geekmomprojects/CubeSphere/Orb4x4/Pictures/CubeBodyAndLidLabelled.JPG

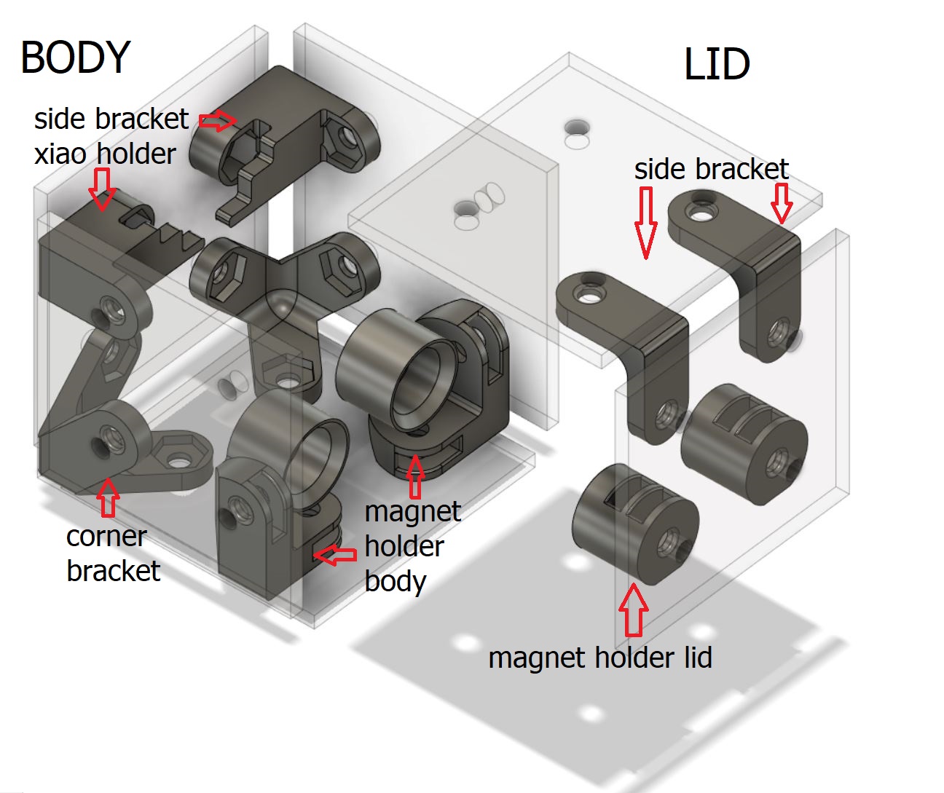
Orb4x4/Pictures/CubeBodyAndLidLabelled.JPG
