geekmomprojects/CubeSphere/Orb4x4/Pictures/CubeBodyWithoutBatteryHolder.JPG

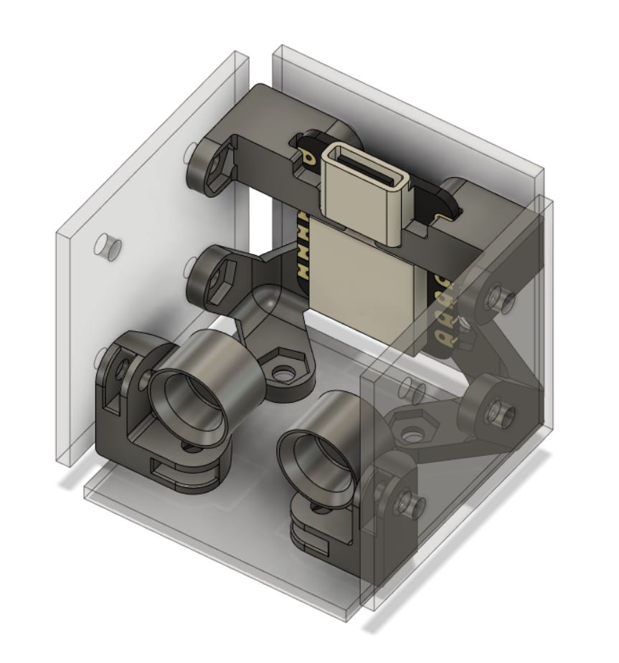
Orb4x4/Pictures/CubeBodyWithoutBatteryHolder.JPG
