geekmomprojects/CubeSphere/Orb4x4/Pictures/CubeLidWithConnectors.JPG

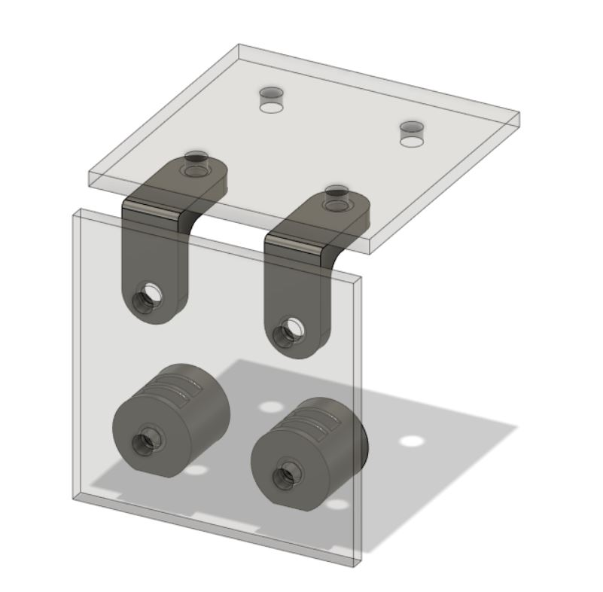
Orb4x4/Pictures/CubeLidWithConnectors.JPG
