geekmomprojects/CubeSphere/Orb5x5/Pictures/Orb5x5.JPG

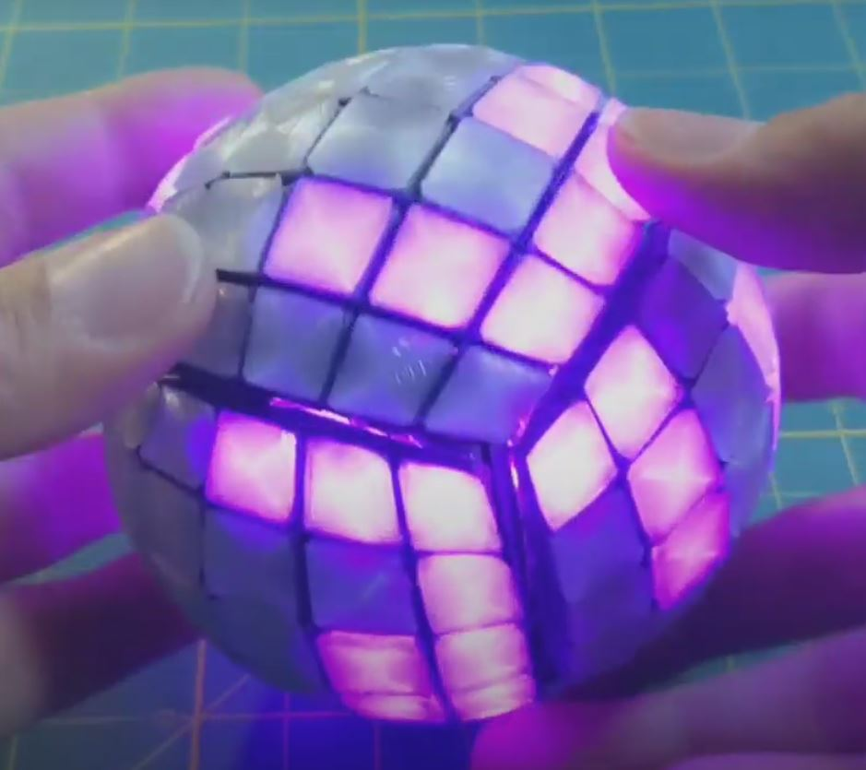
Orb5x5/Pictures/Orb5x5.JPG
