geekmomprojects/CubeSphere/Orb5x5/Pictures/OrbTiltPattern5x5.jpg

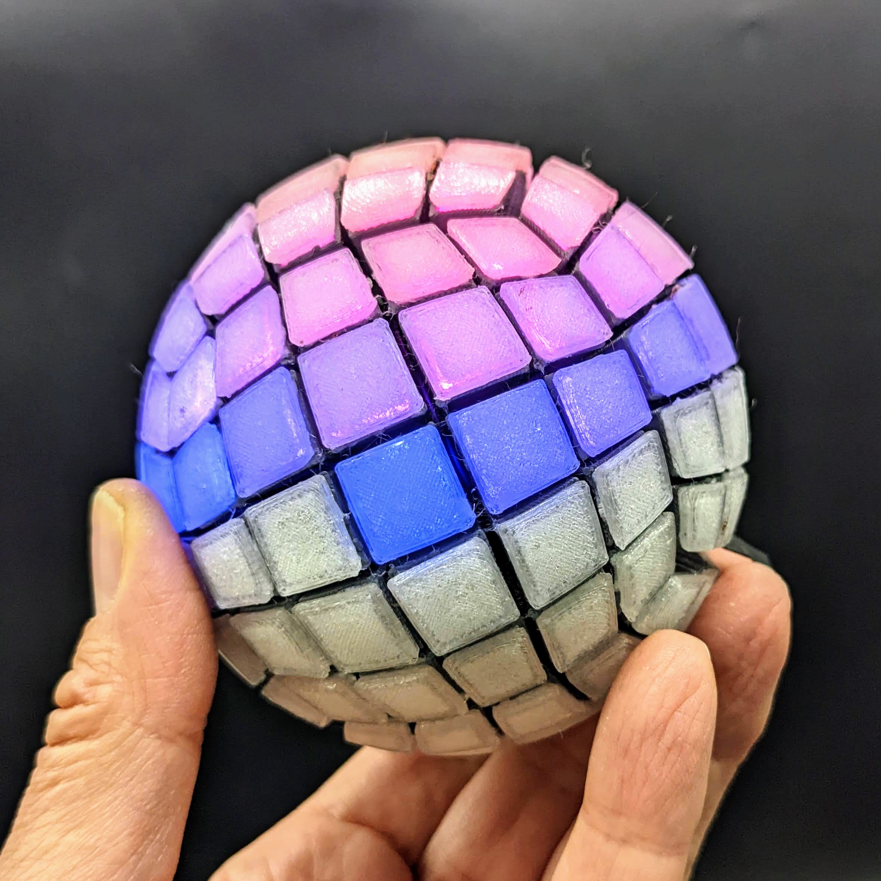
Orb5x5/Pictures/OrbTiltPattern5x5.jpg
