geekmomprojects/CubeSphere/Orb5x5/Pictures/OrbWithCube5x5.jpg

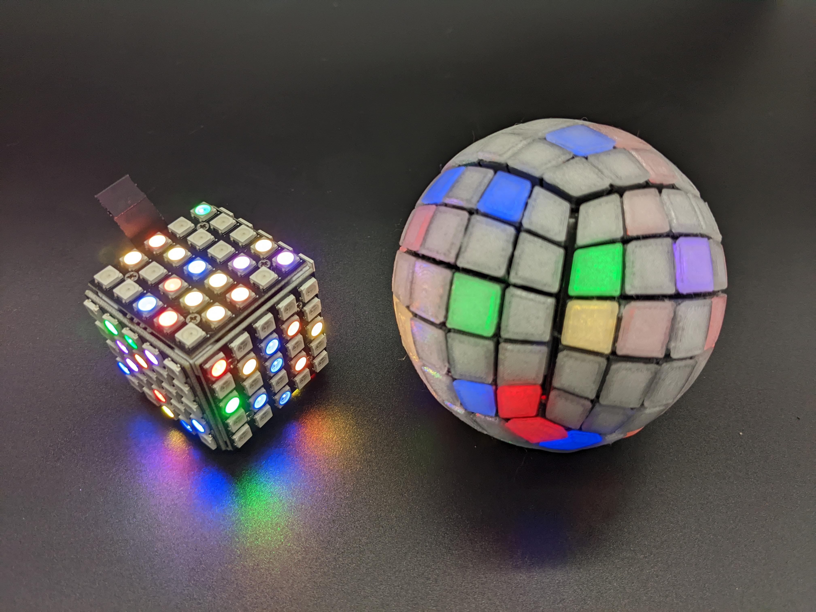
Orb5x5/Pictures/OrbWithCube5x5.jpg
