geekmomprojects/CubeSphere/Orb8x8/SK9822/Pictures/ConnectorsOnly.JPG

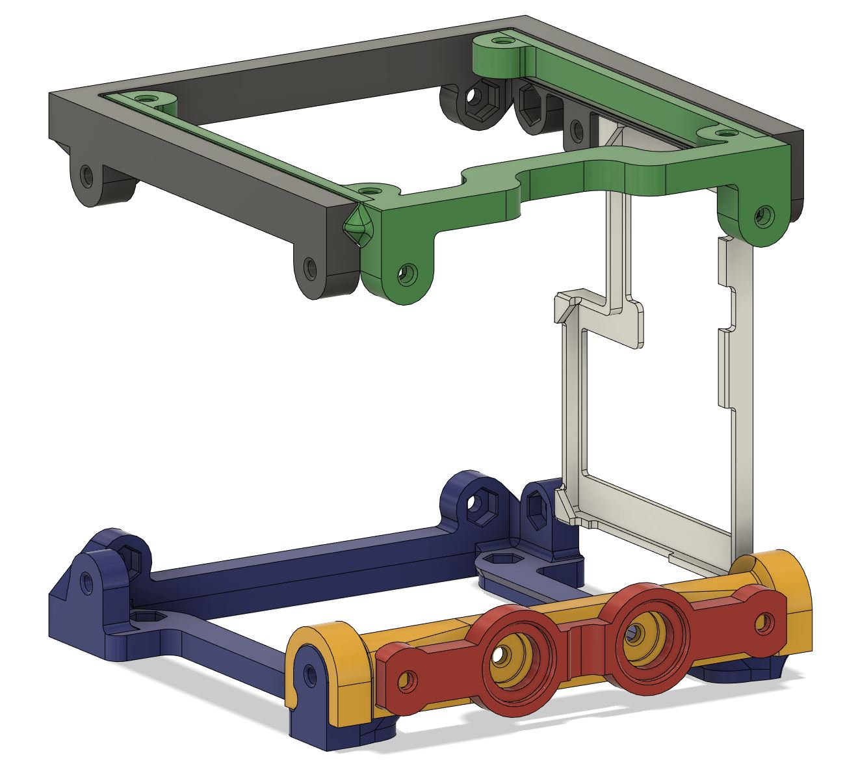
Orb8x8/SK9822/Pictures/ConnectorsOnly.JPG
