geekmomprojects/CubeSphere/Orb8x8/SK9822/Pictures/MatrixBodyWithConnectors.JPG

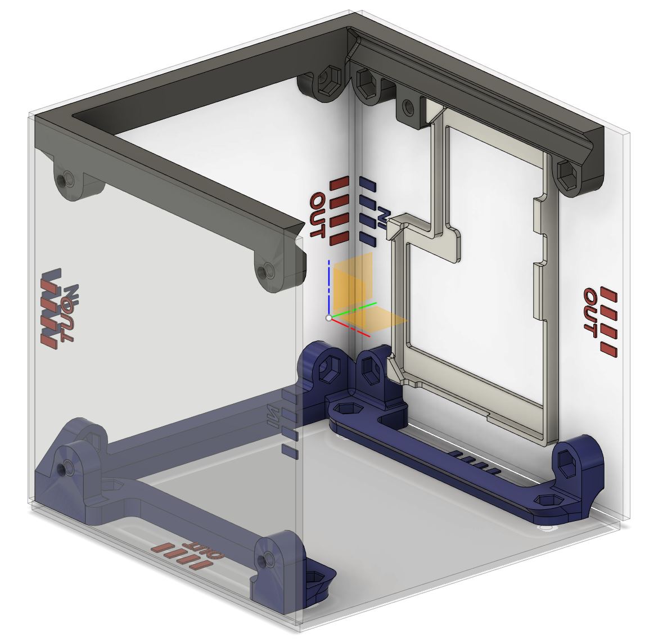
Orb8x8/SK9822/Pictures/MatrixBodyWithConnectors.JPG
