geekmomprojects/CubeSphere/Orb8x8/SK9822/Pictures/MatrixBodyWithConnectorsAndLatch.JPG

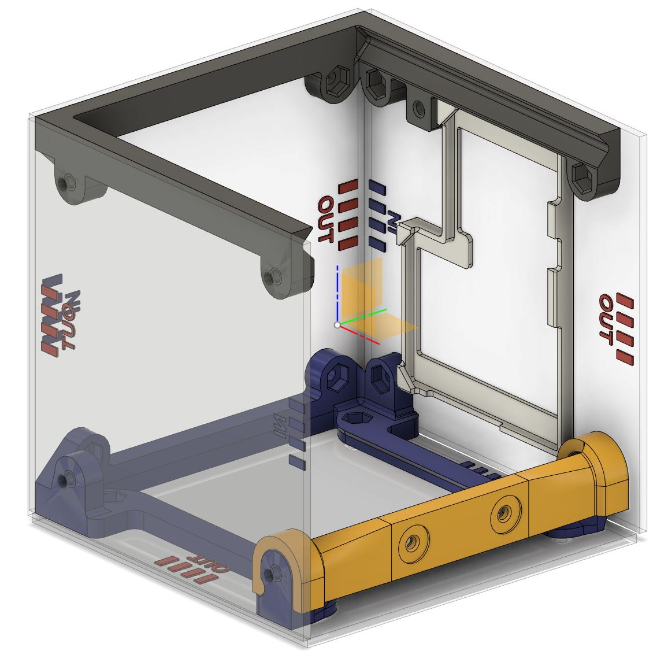
Orb8x8/SK9822/Pictures/MatrixBodyWithConnectorsAndLatch.JPG
