geekmomprojects/CubeSphere/Orb8x8/WS2812/Pictures/ConnectorsOnly.JPG

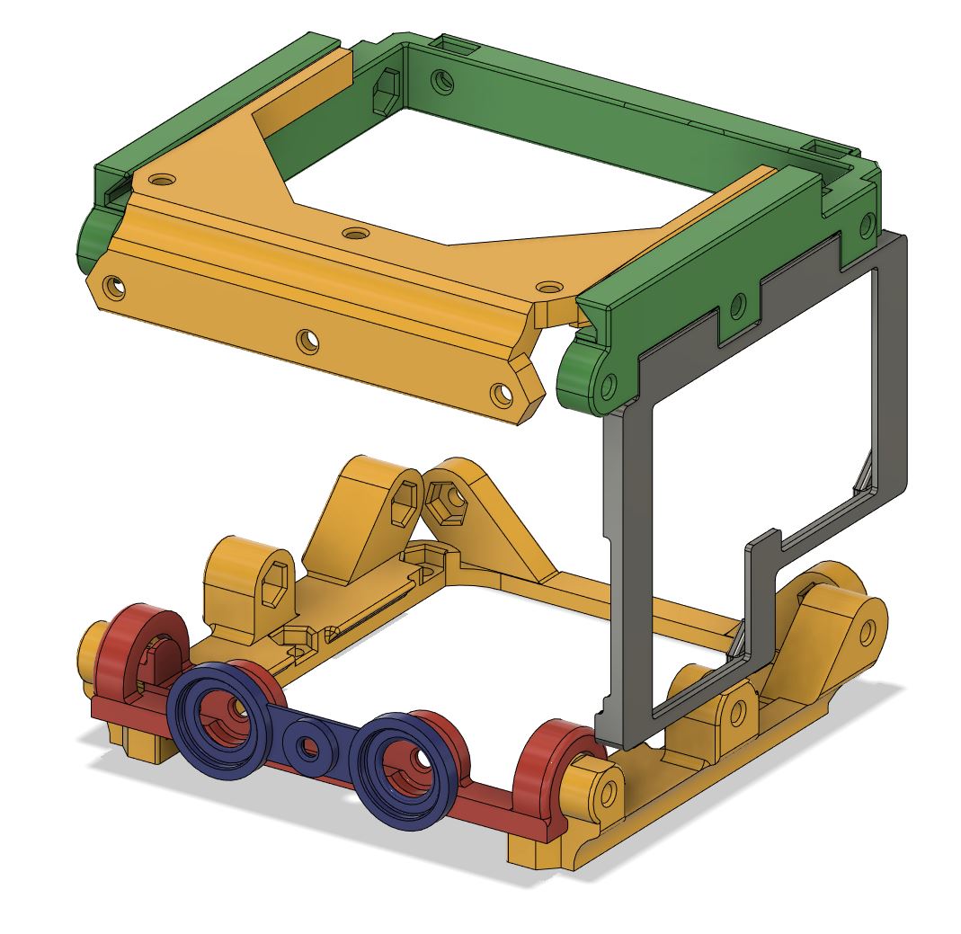
Orb8x8/WS2812/Pictures/ConnectorsOnly.JPG
