geekmomprojects/CubeSphere/Orb8x8/WS2812/Pictures/MatrixBodyLayout.JPG

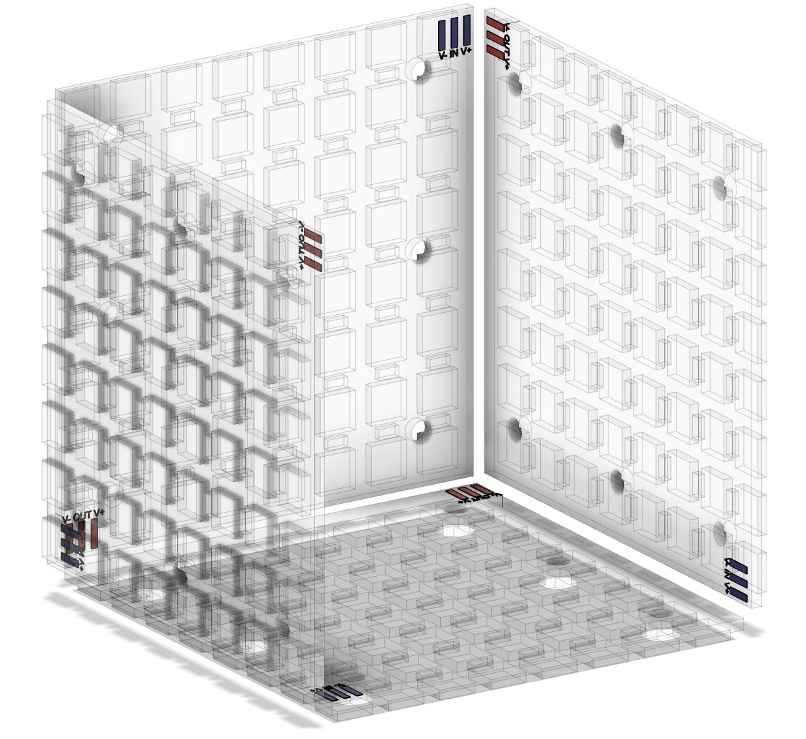
Orb8x8/WS2812/Pictures/MatrixBodyLayout.JPG
