geekmomprojects/CubeSphere/Orb8x8/WS2812/Pictures/MatrixBodyWithoutLock.JPG

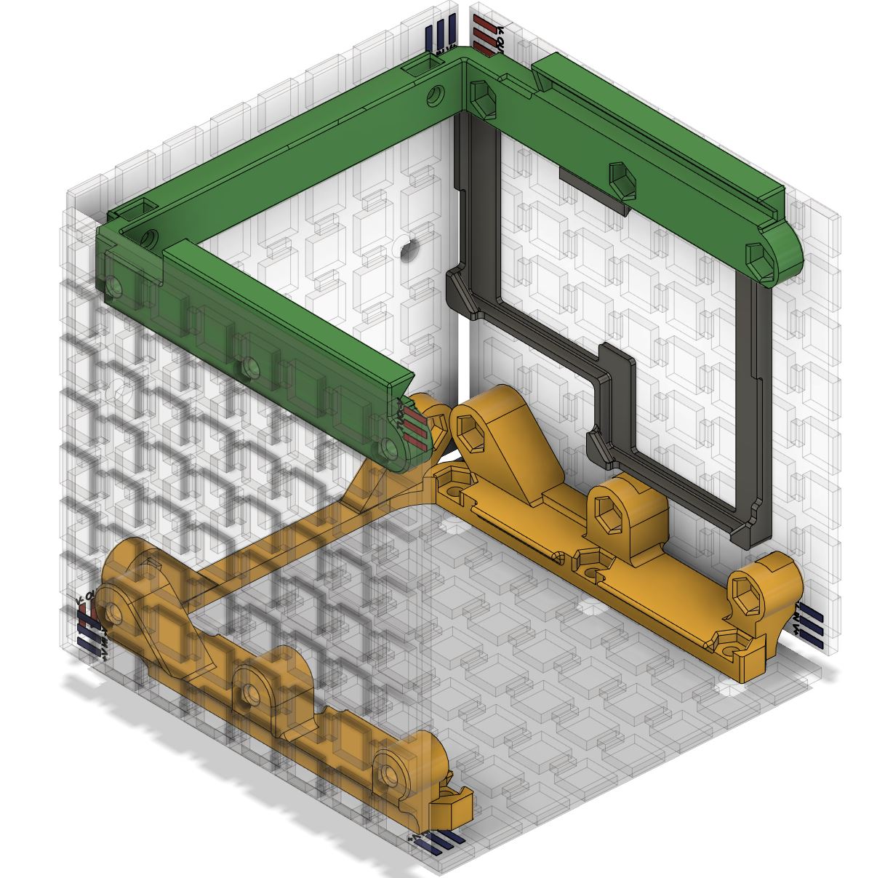
Orb8x8/WS2812/Pictures/MatrixBodyWithoutLock.JPG
