geekmomprojects/CubeSphere/Orb8x8/WS2812/Pictures/MatrixLid.JPG

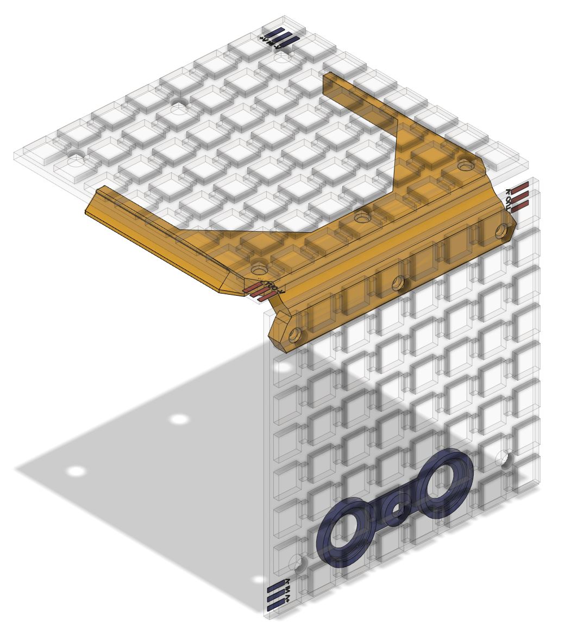
Orb8x8/WS2812/Pictures/MatrixLid.JPG
