geekmomprojects/CubeSphere/Orb8x8/WS2812/Pictures/Orb8x8.jpg

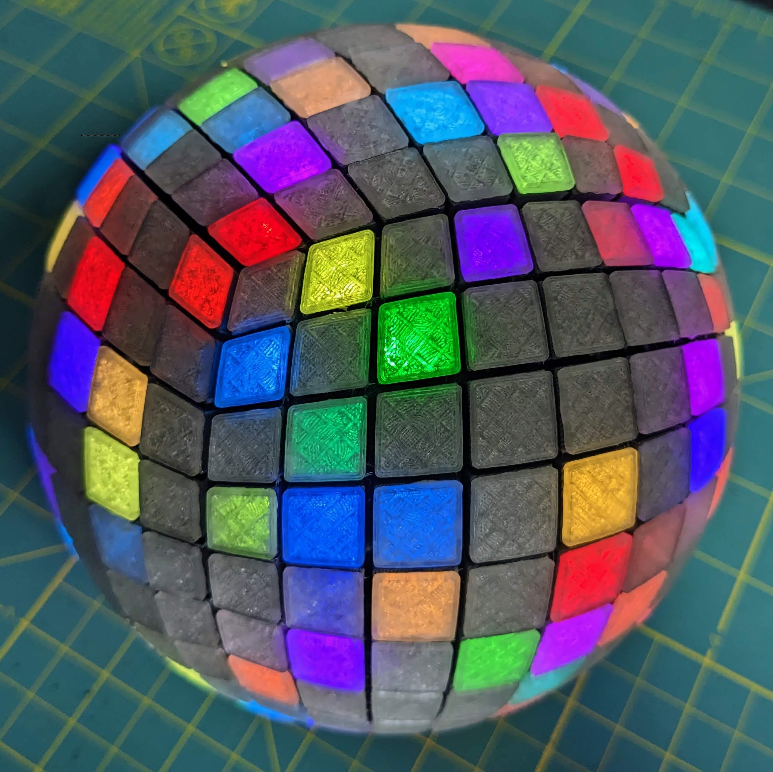
Orb8x8/WS2812/Pictures/Orb8x8.jpg
