geekmomprojects/CubeSphere/Orb5x5/Design/BatteryHolder16340.stl

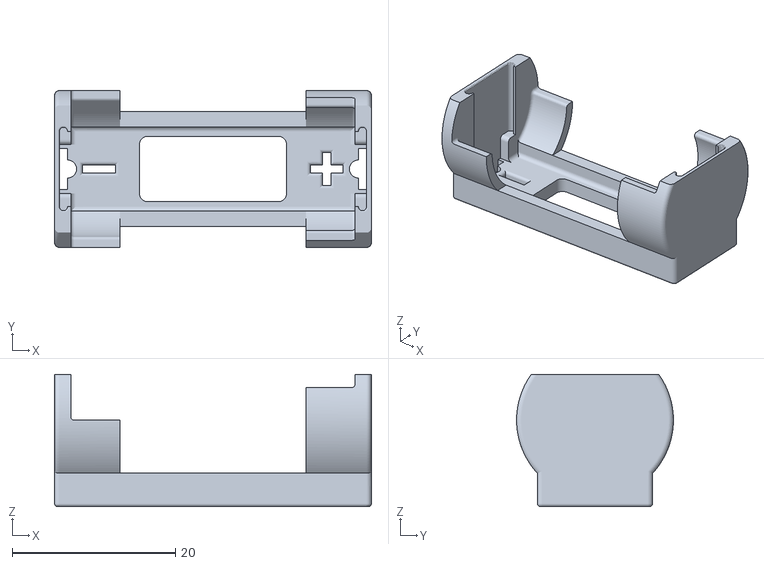
[picture p46: CAD file, 2022-10-06]
Orb5x5/Design/BatteryHolder16340.stl
38.8 x 19.2 x 16.2
