geekmomprojects/CubeSphere/Orb4x4_V2/Design/BatHolder.stl

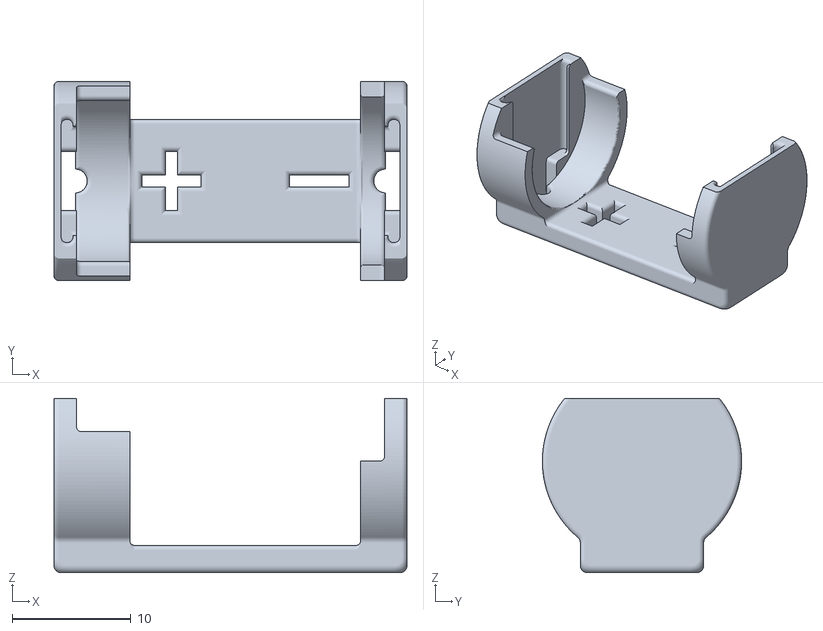
[picture p47: CAD file, 2022-10-06, an earlier design]
Orb4x4_V2/Design/BatHolder.stl
29.8 x 16.8 x 14.7
