geekmomprojects/CubeSphere/Orb4x4_V2/Design/Shell4x4V2.stl

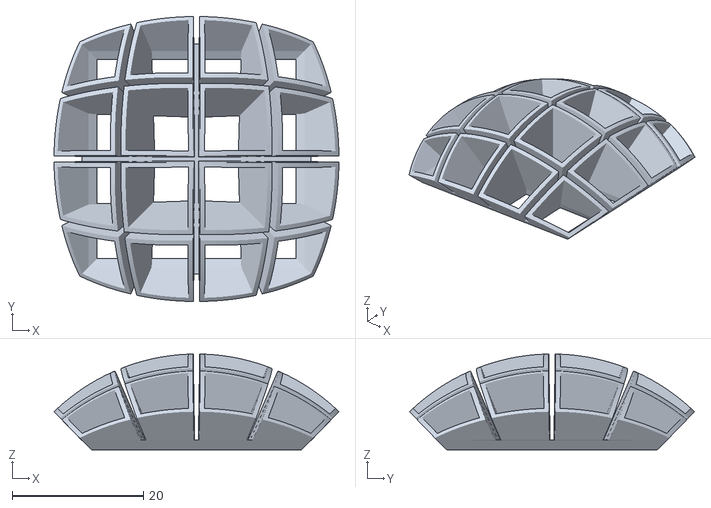
[picture p48: CAD file, 2022-10-06, an earlier design]
Orb4x4_V2/Design/Shell4x4V2.stl
43.5 x 43.5 x 14.6
